fabrizio-indirli/WhistleDrivenRobot/documentation/files/images/ArduinoConnection.png

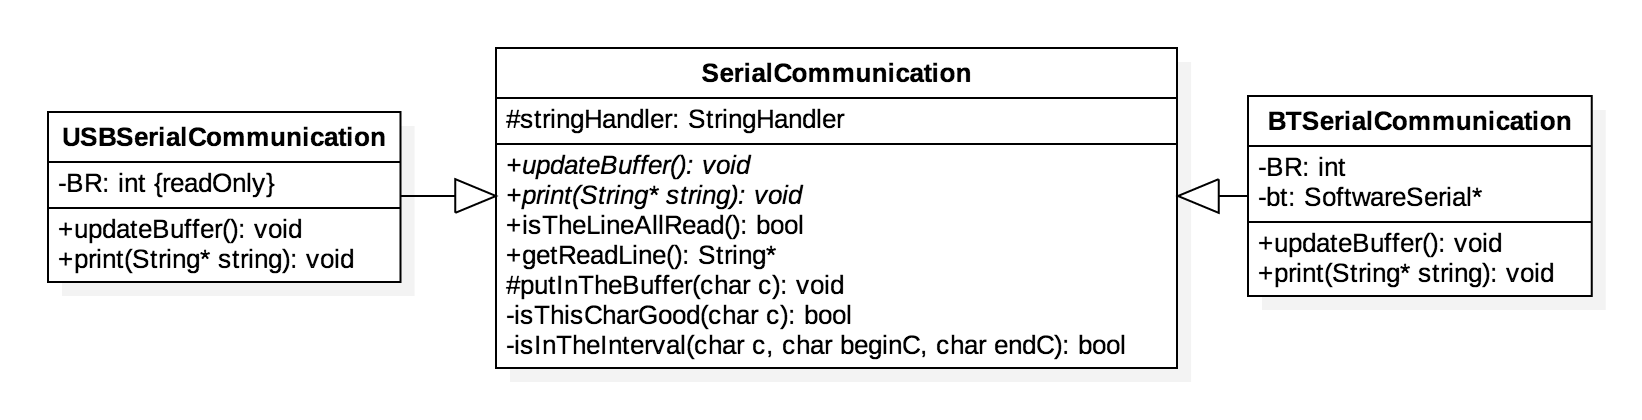
documentation/files/images/ArduinoConnection.png
