fabrizio-indirli/WhistleDrivenRobot/documentation/files/images/display_on.jpg

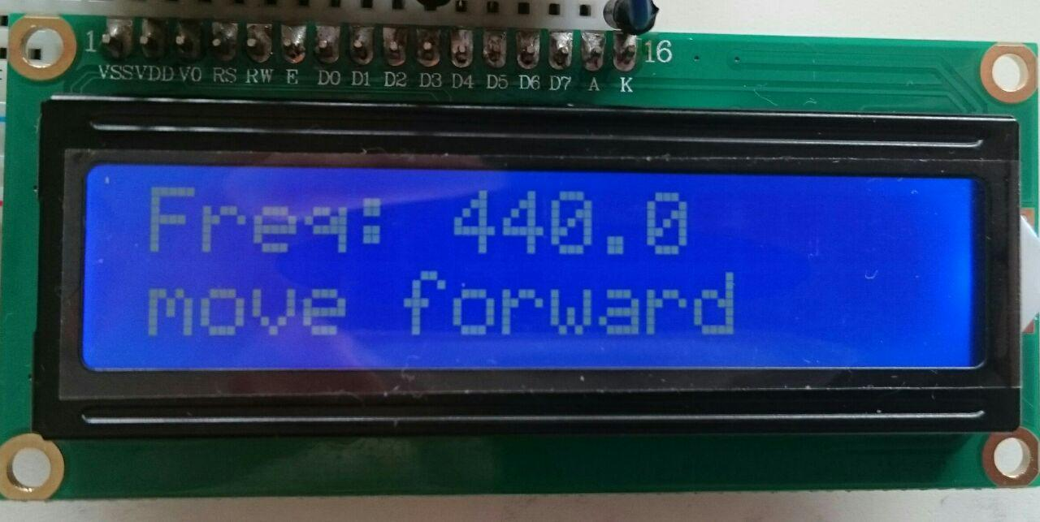
documentation/files/images/display_on.jpg
