fabrizio-indirli/WhistleDrivenRobot/documentation/files/images/freqAcquisitionUML.png

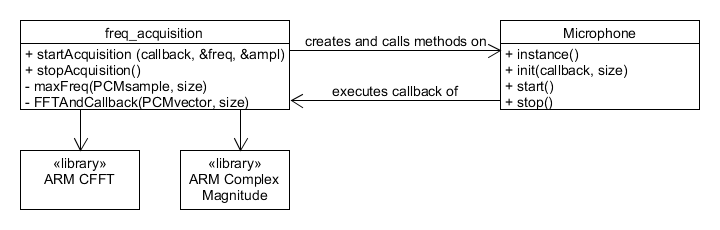
documentation/files/images/freqAcquisitionUML.png
