fabrizio-indirli/WhistleDrivenRobot/documentation/files/images/SystemStructure.png

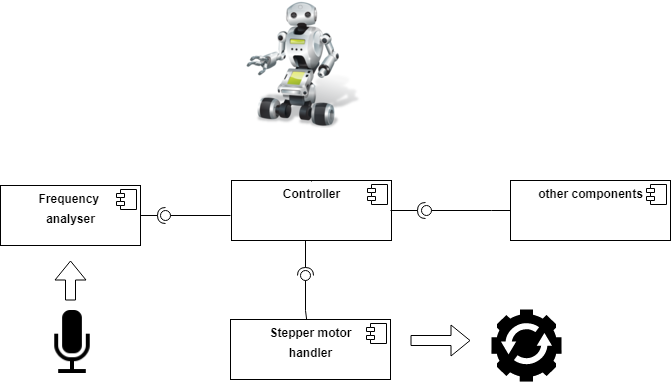
documentation/files/images/SystemStructure.png
