fabrizio-indirli/WhistleDrivenRobot/photos/IMG_20190316_165451870.jpg

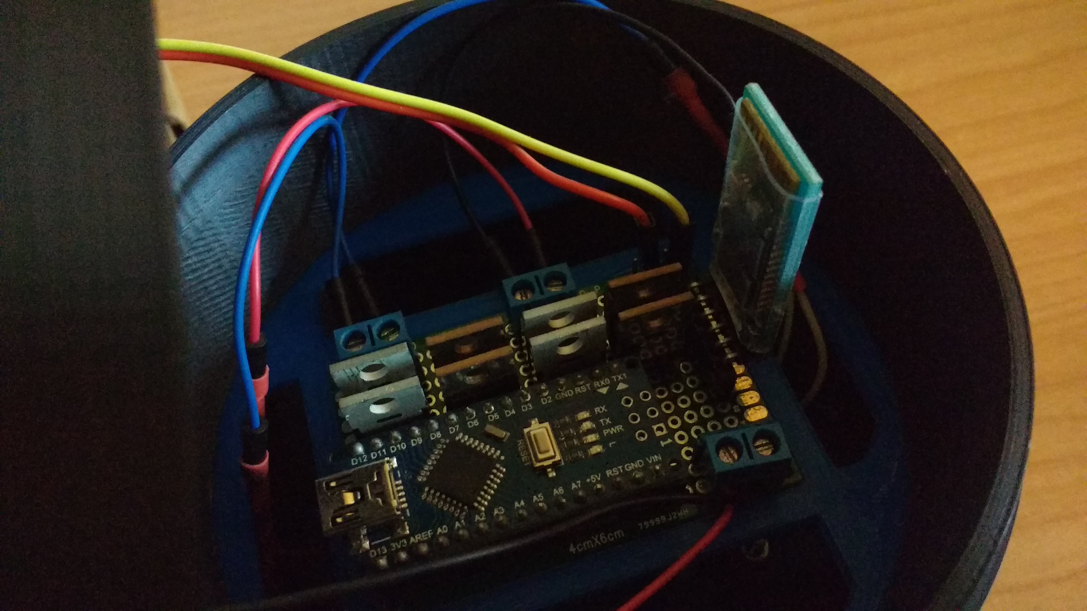
photos/IMG_20190316_165451870.jpg
