fabrizio-indirli/WhistleDrivenRobot/photos/IMG_20190316_165754348.jpg

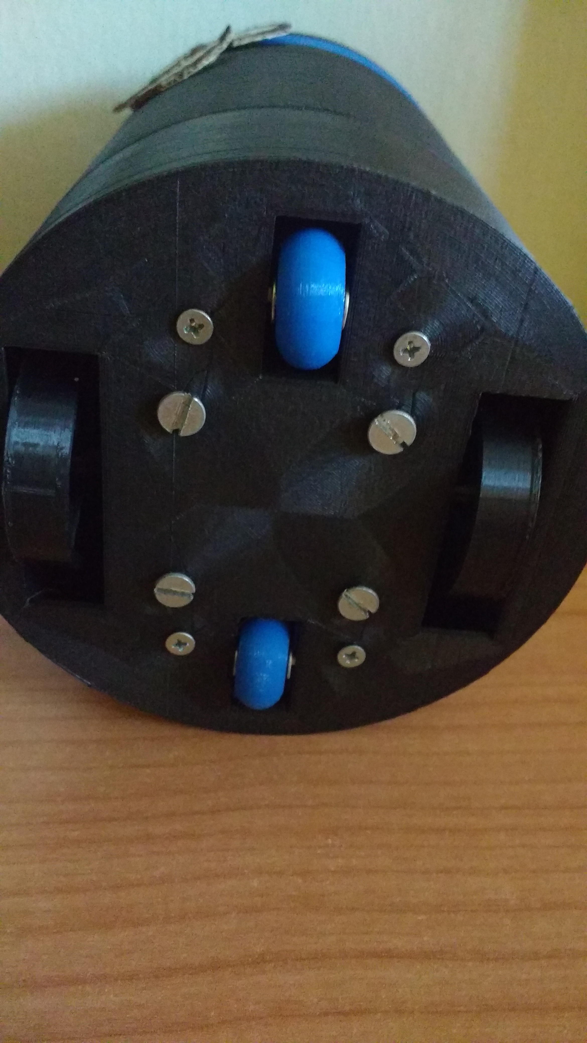
photos/IMG_20190316_165754348.jpg
